mgoegel/ec1834-fdc-board/EC1834_FDC.kicad_sch

## KiCad design EC1834_FDC.kicad_sch (2025-08-20)

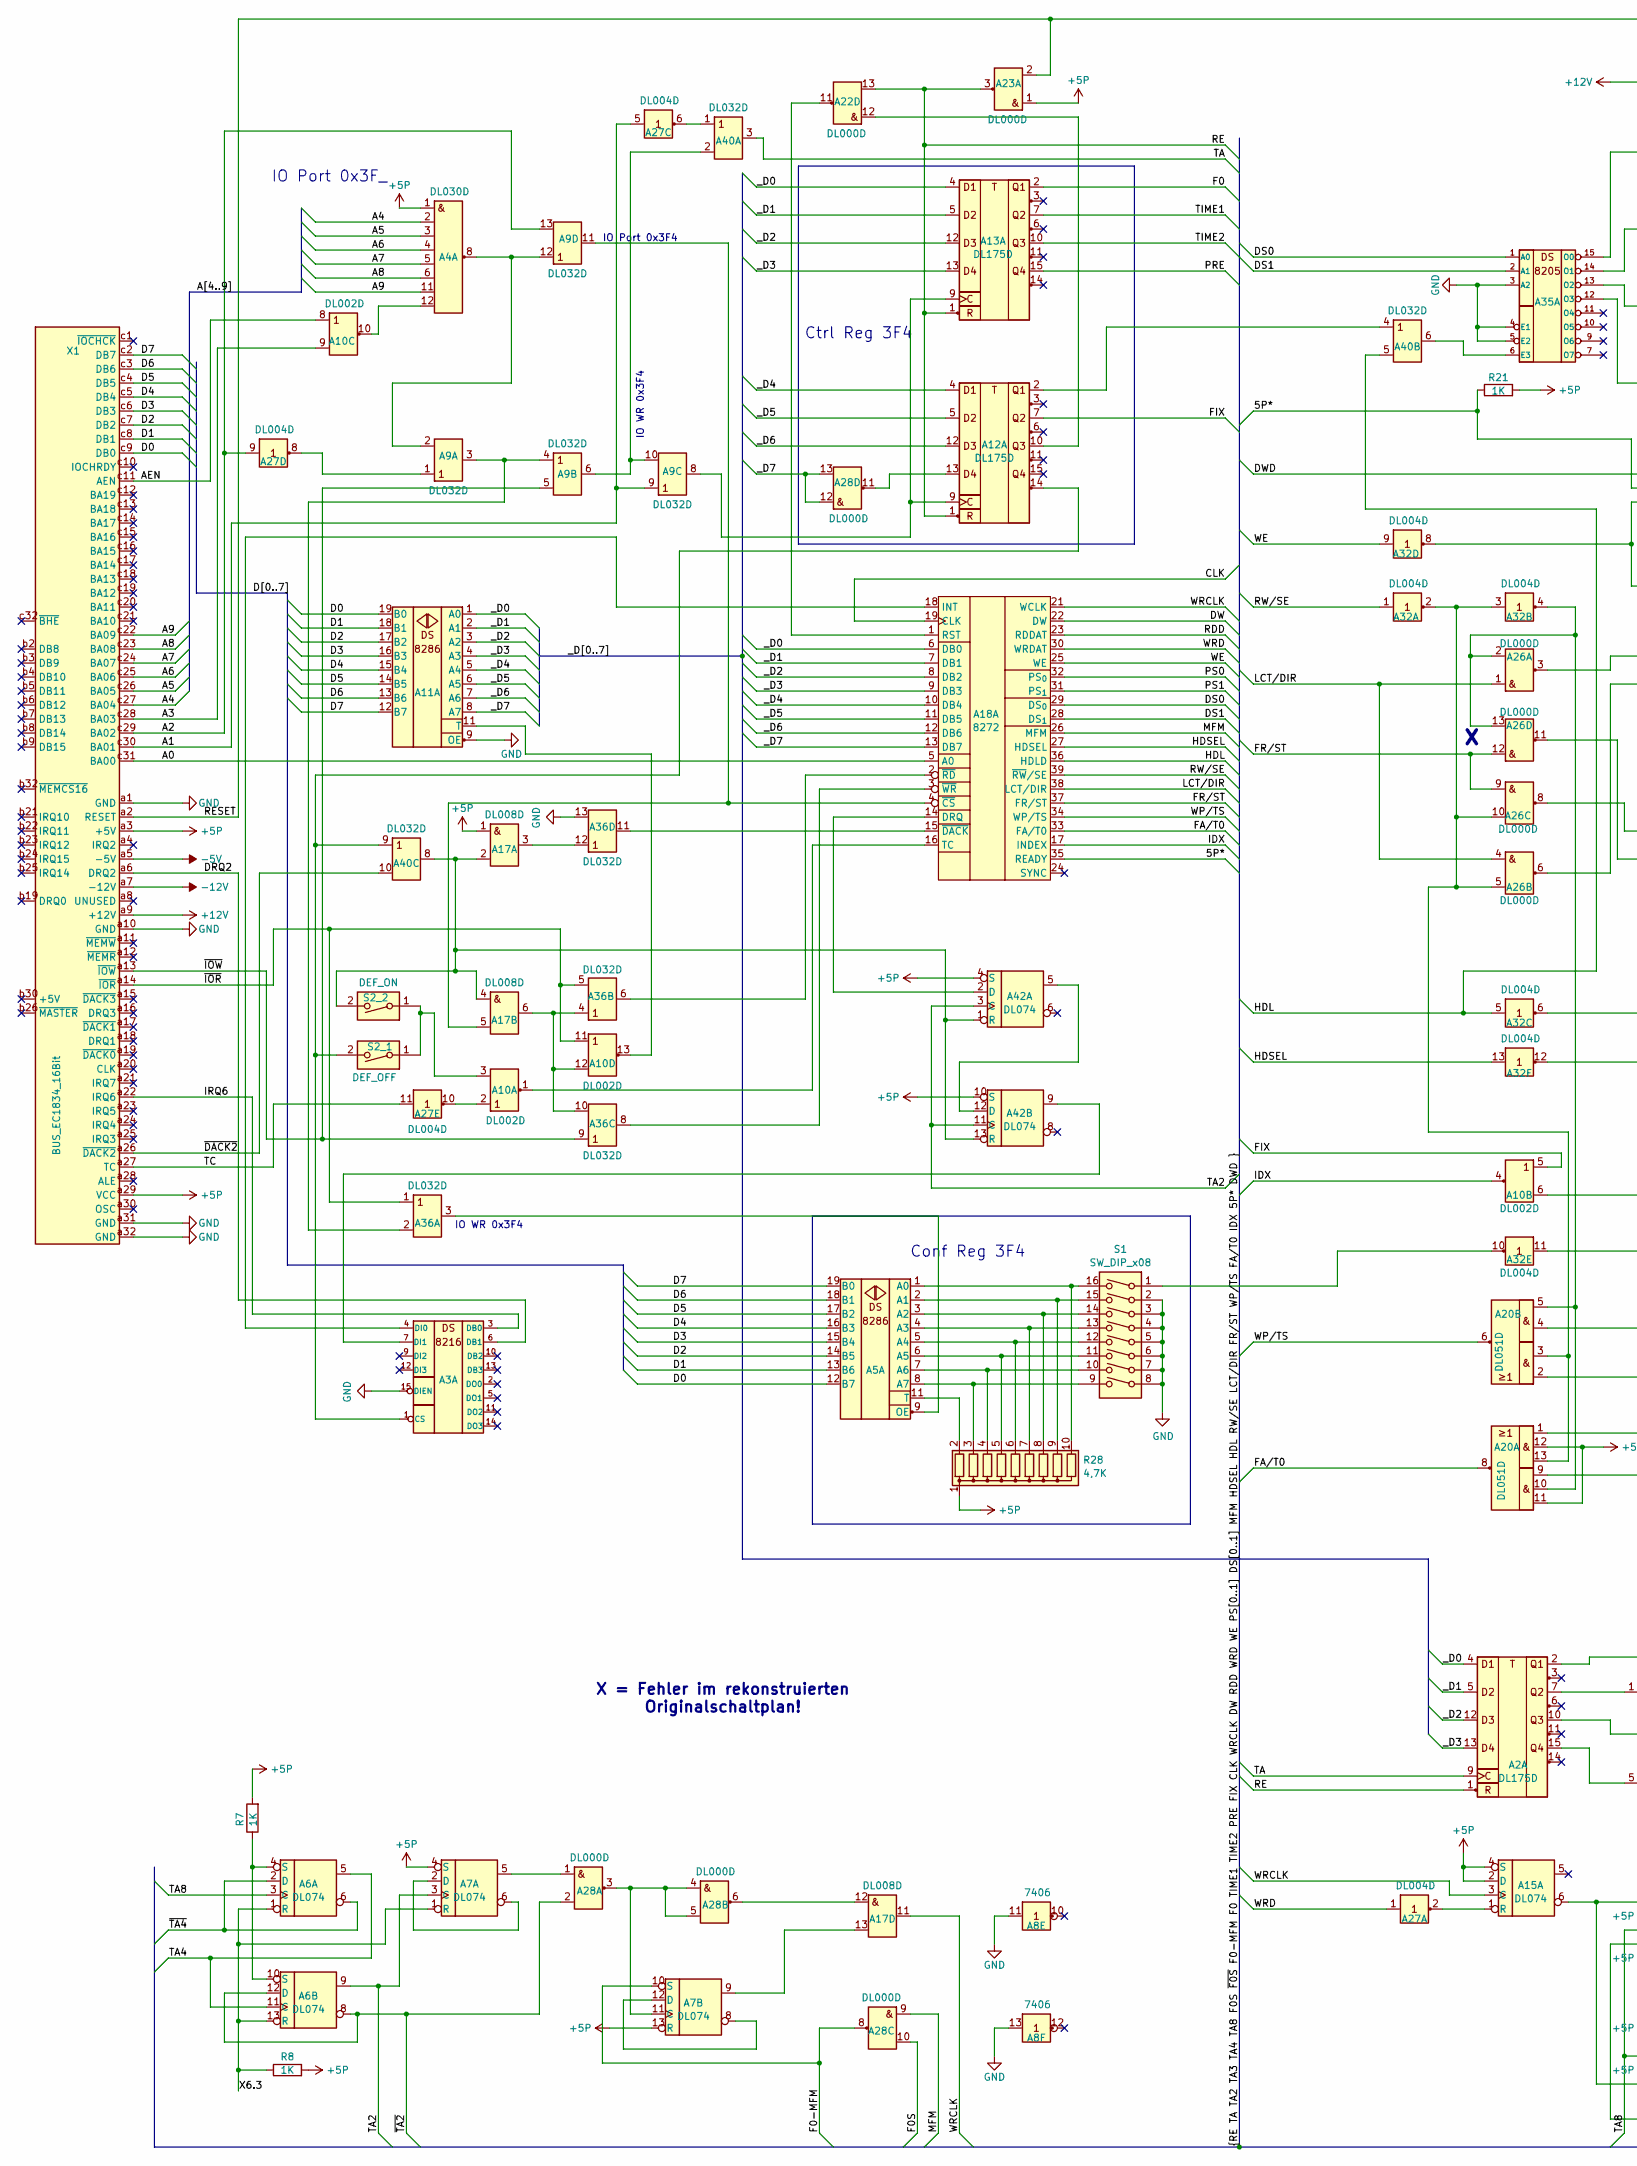
[picture p4: schematic EC1834_FDC.kicad_sch, part in row 1, column 1]

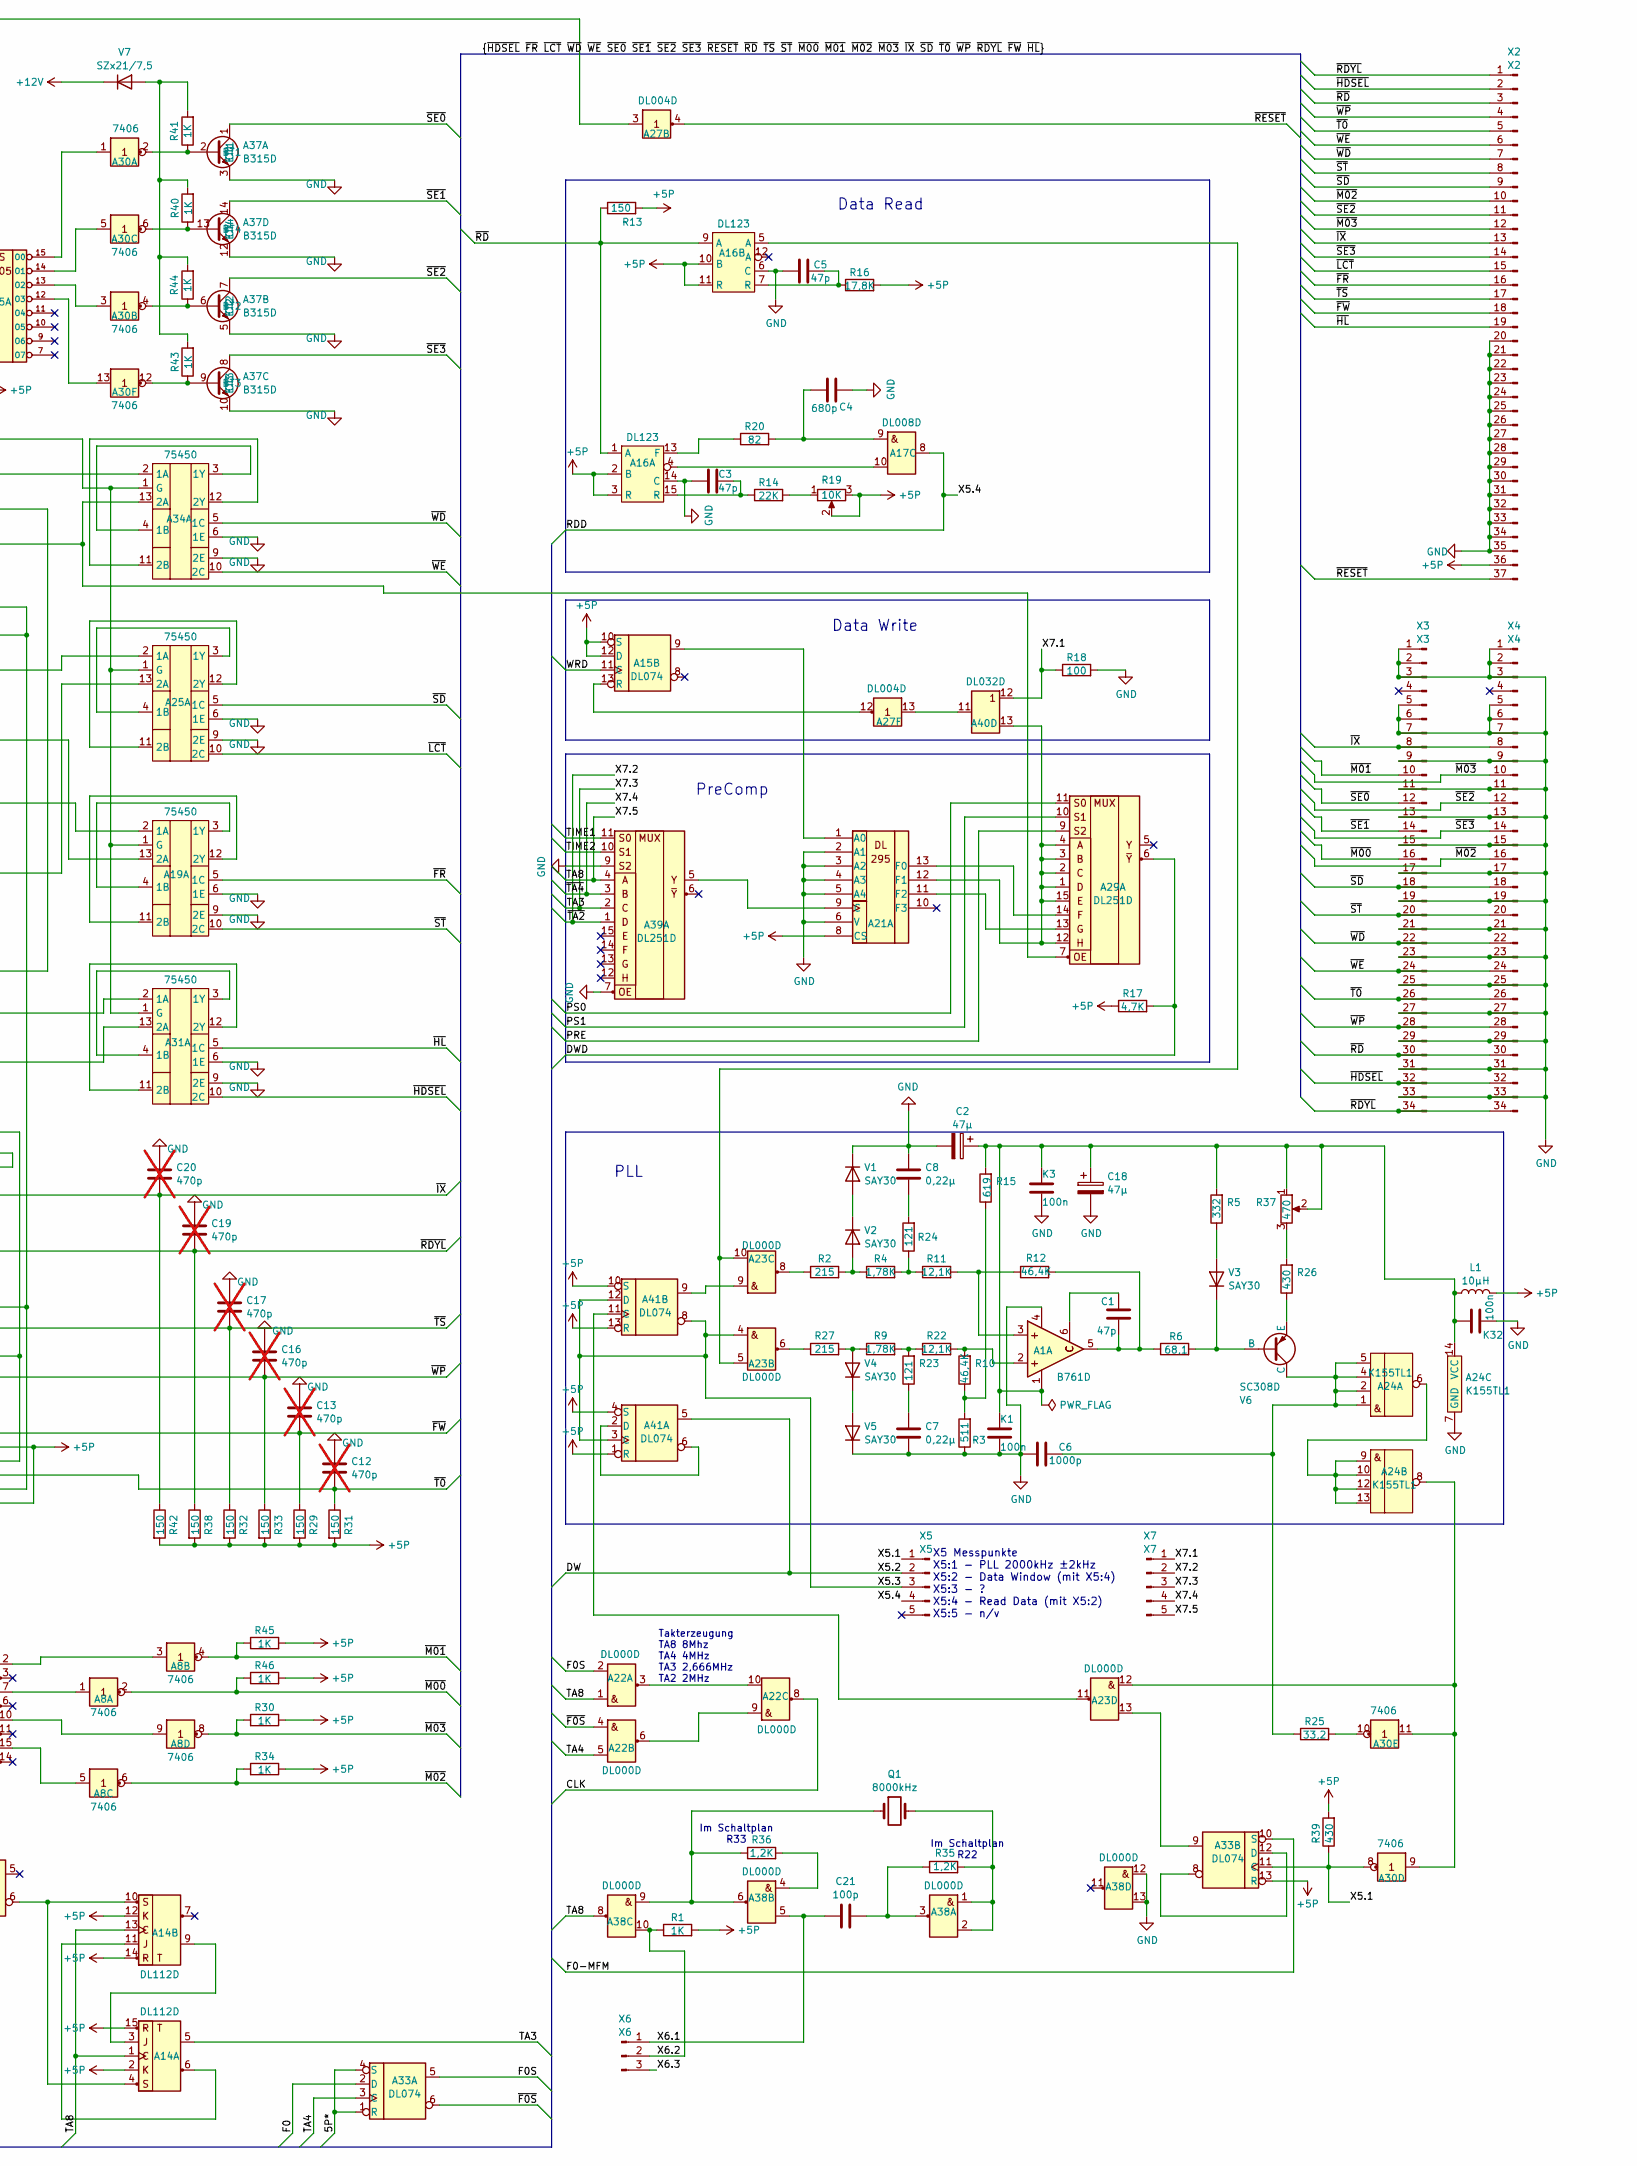
[picture p5: schematic EC1834_FDC.kicad_sch, part in row 1, column 2]

Parts:
A1: B761D; DIP-6_W7.62mm
A2, A12, A13: DL175D; DIP-16_W7.62mm
A3: DS8216; DIP-16_W7.62mm
A4: DL030D; DIP-14_W7.62mm
A5, A11: DS8286D; DIP-20_W7.62mm
A6, A7, A15, A33, A41, A42: DL074; DIP-14_W7.62mm
A8, A30: 7406; DIP-14_W7.62mm
A9, A36, A40: DL032D; DIP-14_W7.62mm
A10: DL002D; DIP-14_W7.62mm
A14: DL112D; DIP-16_W7.62mm
A16: DL123; DIP-16_W7.62mm
A17: DL008D; DIP-14_W7.62mm
A18: 8272; DIP-40_W15.24mm
A19, A25, A31, A34: 75450; DIP-14_W7.62mm
A20: DL051D; DIP-14_W7.62mm
A21: DL295; DIP-14_W7.62mm
A22, A23, A26, A28, A38: DL000D; DIP-14_W7.62mm
A24: K155TL1; DIP-14_W7.62mm
A27, A32: DL004D; DIP-14_W7.62mm
A29, A39: DL251D; DIP-16_W7.62mm
A35: DS8205; DIP-16_W7.62mm
A37: B315D; DIP-14_W7.62mm
C1, C3, C5: 47p; C_Disc_D4.3mm_W1.9mm_P5.00mm
C2, C18: 47µ; CP_Radial_Tantal_D5.0mm_P5.00mm
C4: 680p; C_Disc_D4.3mm_W1.9mm_P5.00mm
C6: 1000p; CP_Axial_L11.0mm_D5.0mm_P18.00mm_Horizontal
C7, C8: 0,22µ; CP_Axial_L18.0mm_D6.5mm_P25.00mm_Horizontal
C12, C13, C16, C17, C19, C20: 470p; C_Disc_D4.3mm_W1.9mm_P5.00mm; not fitted
C21: 100p; C_Disc_D4.3mm_W1.9mm_P5.00mm
K1, K3, K32: 100n; C_Disc_D4.3mm_W1.9mm_P5.00mm
L1: 10µH; L_Axial_L9.5mm_D4.0mm_P12.70mm_Horizontal_Fastron_SMCC
Q1: 8000kHz; Crystal_HC49-U_Horizontal
R1, R7, R8, R21, R30, R34, R40, R41, R43, R44, R45, R46: 1K; R_Axial_L9.0mm_D1.8mm_P12.70mm_Horizontal
R2, R27: 215; R_Axial_L9.0mm_D1.8mm_P12.70mm_Horizontal
R3: 511; R_Axial_L9.0mm_D1.8mm_P12.70mm_Horizontal
R4, R9: 1,78K; R_Axial_L9.0mm_D1.8mm_P12.70mm_Horizontal
R5: 332; R_Axial_L9.0mm_D1.8mm_P12.70mm_Horizontal
R6: 68,1; R_Axial_L9.0mm_D1.8mm_P12.70mm_Horizontal
R10, R12: 46,4K; R_Axial_L9.0mm_D1.8mm_P12.70mm_Horizontal
R11, R22: 12,1K; R_Axial_L9.0mm_D1.8mm_P12.70mm_Horizontal
R13, R29, R31, R32, R33, R38, R42: 150; R_Axial_L9.0mm_D1.8mm_P12.70mm_Horizontal
R14: 22K; R_Axial_L9.0mm_D1.8mm_P12.70mm_Horizontal
R15: 619; R_Axial_L9.0mm_D1.8mm_P12.70mm_Horizontal
R16: 17,8K; R_Axial_L9.0mm_D1.8mm_P12.70mm_Horizontal
R17: 4,7K; R_Axial_L9.0mm_D1.8mm_P12.70mm_Horizontal
R18: 100; R_Axial_L9.0mm_D1.8mm_P12.70mm_Horizontal
R19: 10K; Potentiometer_ACP_CA6-H2,5_Horizontal
R20: 82; R_Axial_L9.0mm_D1.8mm_P12.70mm_Horizontal
R23, R24: 121; R_Axial_L9.0mm_D1.8mm_P12.70mm_Horizontal
R25: 33,2; R_Axial_L9.0mm_D1.8mm_P12.70mm_Horizontal
R26, R39: 430; R_Axial_L9.0mm_D1.8mm_P12.70mm_Horizontal
R28: 4,7K; R_Array_SIP10
R35, R36: 1,2K; R_Axial_L9.0mm_D1.8mm_P12.70mm_Horizontal
R37: 470; Potentiometer_ACP_CA6-H2,5_Horizontal
S1: SW_DIP_x08; SW_DIP_SPSTx08_Slide_6.7x21.88mm_W7.62mm_P2.54mm_LowProfile
S2_1: DEF_OFF; SW_DIP_SPSTx01_Slide_9.78x4.72mm_W7.62mm_P2.54mm
S2_2: DEF_ON; SW_DIP_SPSTx01_Slide_9.78x4.72mm_W7.62mm_P2.54mm
V1, V2, V3, V4, V5: SAY30; TO-92-2
V6: SC308D; TO-92_Inline_Wide
V7: SZx21/7,5; TO-92-2
X1: BUS_EC1834_16Bit; DIN41612_C_3x32_Male_Horizontal_THT
X2: X2; DSUB-37_Socket_Horizontal_P2.77x2.84mm_EdgePinOffset9.90mm_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
X3: X3; IDC-Header_2x17_P2.54mm_Vertical
X4: X4; IDC-Header_2x17_P2.54mm_Vertical
X5: X5; Molex_KK-254_AE-6410-05A_1x05_P2.54mm_Vertical
X6: X6; Molex_KK-254_AE-6410-03A_1x03_P2.54mm_Vertical
X7: X7; Molex_KK-254_AE-6410-05A_1x05_P2.54mm_Vertical

Connections:
5P*: A18.35 (READY), A19.1 (G), A25.1 (G), A31.1 (G), A33.1 (R), A33.4 (S), A34.1 (G), R21.1
+5P: A4.1 (A), A7.4 (S), A7.13 (R), A14.2 (K1), A14.12 (K2), A14.14 (R2), A14.15 (R1), A15.2 (D), A15.4 (S), A15.10 (S), A15.12 (D), A16.2 (B), A16.3 (R), A16.10 (B), A16.11 (R), A17.1 (A1), A20.11 (1F), A20.12 (1B), A21.8 (CS), A23.1 (A1), A33.13 (R), A41.1 (R), A41.4 (S), A41.10 (S), A41.13 (R), A42.4 (S), A42.10 (S), L1.2, R1.2, R7.2, R8.2, R13.2, R16.2, R17.1, R19.2, R19.3, R21.2, R28.1 (common), R29.2, R30.1, R31.2, R32.2, R33.2, R34.1, R38.2, R39.2, R42.2, R45.2, R46.2, X1.a3 (+5V), X1.a29 (VCC), X2.36
+12V: V7.1 (K), X1.a9 (+12V)
-5V: X1.a5 (-5V)
-12V: X1.a7 (-12V)
A0: A18.5 (A0), X1.c31 (BA00)
A1: A9.9 (A3), A27.5 (A3), X1.c30 (BA01)
A2: A9.13 (B4), A27.9 (A4), X1.c29 (BA02)
A3: A10.9 (B3), X1.c28 (BA03)
A4: A4.2 (B), X1.c27 (BA04)
A5: A4.3 (C), X1.c26 (BA05)
A6: A4.4 (D), X1.c25 (BA06)
A7: A4.5 (E), X1.c24 (BA07)
A8: A4.6 (F), X1.c23 (BA08)
A9: A4.11 (G), X1.c22 (BA09)
AEN: A10.8 (A3), X1.c11 (AEN)
CLK: A18.19 (CLK), A22.8 (Y3)
D0: A5.12 (B7), A11.19 (B0), X1.c9 (DB0)
D1: A5.13 (B6), A11.18 (B1), X1.c8 (DB1)
D2: A5.14 (B5), A11.17 (B2), X1.c7 (DB2)
D3: A5.15 (B4), A11.16 (B3), X1.c6 (DB3)
D4: A5.16 (B3), A11.15 (B4), X1.c5 (DB4)
D5: A5.17 (B2), A11.14 (B5), X1.c4 (DB5)
D6: A5.18 (B1), A11.13 (B6), X1.c3 (DB6)
D7: A5.19 (B0), A11.12 (B7), X1.c2 (DB7)
DRQ2: A3.6 (DB1), X1.a6 (DRQ2)
DS0: A18.29 (DS_{0}), A35.1 (A0)
DS1: A18.28 (DS_{1}), A35.2 (A1)
DW: A18.22 (DW), A41.5, X5.2
DWD: A29.6 (~Y), A34.2 (1A), R17.2
F0: A13.2 (Q1), A33.2 (D)
F0-MFM: A7.10 (S), A28.8 (Y3), A33.10 (S)
F0S: A22.2 (B1), A28.10 (B3), A33.5
FA/T0: A18.33 (FA/T0), A20.8 (1Y)
FIX: A10.5 (A2), A12.7 (Q2)
FR/ST: A18.37 (FR/ST), A26.9 (A3), A26.12 (A4)
GND: A1.4 (-), A3.15 (DIEN), A8.11 (A5), A8.13 (A6), A11.9 (OE), A16.6 (C), A16.14 (C), A19.6 (1E), A19.9 (2E), A21.2 (A1), A21.3 (A2), A21.4 (A3), A21.5 (A4), A21.6 (V), A24.7 (GND), A25.6 (1E), A25.9 (2E), A31.6 (1E), A31.9 (2E), A34.6 (1E), A34.9 (2E), A35.3 (A2), A35.4 (E1), A35.5 (E2), A36.13 (B4), A37.3 (ET1), A37.5 (ET2), A37.10 (ET3), A37.12 (ET4), A38.12 (A4), A38.13 (B4), A39.7 (~OE), A39.9 (S2), C2.2, C3.1, C4.1, C5.1, C6.1, C7.1, C8.1, C12.1, C13.1, C16.1, C17.1, C18.2, C19.1, C20.1, K1.2, K3.2, K32.2, R3.1, R18.2, S1.2, S1.3, S1.4, S1.5, S1.6, S1.7, S1.8, V1.1 (K), V5.1 (K), X1.a1 (GND), X1.a10 (GND), X1.a31 (GND), X1.a32 (GND), X2.20, X2.21, X2.22, X2.23, X2.24, X2.25, X2.26, X2.27, X2.28, X2.29, X2.30, X2.31, X2.32, X2.33, X2.34, X2.35, X3.1, X3.2, X3.3, X3.5, X3.6, X3.7, X3.9, X3.11, X3.13, X3.15, X3.17, X3.19, X3.21, X3.23, X3.25, X3.27, X3.29, X3.31, X3.33, X4.1, X4.2, X4.3, X4.5, X4.6, X4.7, X4.9, X4.11, X4.13, X4.15, X4.17, X4.19, X4.21, X4.23, X4.25, X4.27, X4.29, X4.31, X4.33
HDL: A18.36 (HDLD), A32.5 (A3), A40.5 (B2)
HDSEL: A18.27 (HDSEL), A32.13 (A6)
IDX: A10.4 (Y2), A18.17 (INDEX)
IRQ6: A3.3 (DB0), X1.a22 (IRQ6)
LCT/DIR: A18.38 (LCT/DIR), A26.1 (A1), A26.4 (A2)
MFM: A18.26 (MFM), A28.9 (A3)
unnamed: A1.1 (+), A24.14 (VCC), C2.1, C18.1, K1.1, K3.1, K32.1, L1.1, R5.2, R15.2, R37.1, R37.2
unnamed: A1.2 (+), R10.2, R22.2
unnamed: A1.3 (-), R11.2, R12.1
unnamed: A1.5, C1.2, R6.1, R12.2
unnamed: A1.6 (C), C1.1
unnamed: A2.2 (Q1), A8.3 (A2)
unnamed: A2.7 (Q2), A8.1 (A1)
unnamed: A2.10 (Q3), A8.9 (A4)
unnamed: A2.15 (Q4), A8.5 (A3)
unnamed: A3.7 (DI1), A42.9
unnamed: A4.8 (Y), A9.2 (B1), A9.12 (A4)
unnamed: A5.1 (A0), R28.10 (R9), S1.16
unnamed: A5.2 (A1), R28.9 (R8), S1.15
unnamed: A5.3 (A2), R28.8 (R7), S1.14
unnamed: A5.4 (A3), R28.7 (R6), S1.13
unnamed: A5.5 (A4), R28.6 (R5), S1.12
unnamed: A5.6 (A5), R28.5 (R4), S1.11
unnamed: A5.7 (A6), R28.4 (R3), S1.10
unnamed: A5.8 (A7), R28.3 (R2), S1.9
unnamed: A5.11 (T), R28.2 (R1)
unnamed: A6.4 (S), A6.10 (S), R7.1
unnamed: A7.2 (D), A7.6
unnamed: A7.8, A7.12 (D)
unnamed: A10.1 (Y1), A18.16 (TC)
unnamed: A10.2 (A1), A27.10 (Y5)
unnamed: A10.3 (B1), S2_1.1, S2_2.1
unnamed: A4.12 (H), A10.10 (Y3)
unnamed: A10.12 (B4), A17.6 (Y2), A36.4 (A2), A36.10 (B3)
unnamed: A10.13 (Y4), A11.11 (T)
unnamed: A12.2 (Q1), A40.4 (A2)
unnamed: A9.8 (Y3), A12.9 (C), A13.9 (C)
unnamed: A12.10 (Q3), A22.12 (A4)
unnamed: A12.13 (D4), A28.11 (Y4)
unnamed: A3.1 (CS), A12.14 (~Q4), A40.9 (A3), S2_1.2
unnamed: A14.3 (J1), A14.9 (Q2)
unnamed: A14.4 (S1), A14.10 (S2), A15.6
unnamed: A14.6 (/Q1), A14.11 (J2)
unnamed: A15.1 (R), A27.2 (Y1)
unnamed: A15.9, A21.1 (A0)
unnamed: A15.13 (R), A27.12 (Y6)
unnamed: A16.4, A17.10 (B3)
unnamed: A16.5 (A), A23.5 (B2), A23.10 (B3)
unnamed: A16.7 (R), C5.2, R16.1
unnamed: A16.13 (F), R20.1
unnamed: A16.15 (R), C3.2, R14.1
unnamed: A17.2 (B1), A17.4 (A2), A40.8 (Y3), A42.1 (R), A42.13 (R), S2_2.2
unnamed: A17.3 (Y1), A36.12 (A4)
unnamed: A9.11 (Y4), A17.5 (B2), A18.4 (~CS)
unnamed: A17.9 (A3), C4.2, R20.2
unnamed: A17.12 (A4), A28.6 (Y2)
unnamed: A7.9, A17.13 (B4)
unnamed: A18.1 (RST), A22.11 (Y4)
unnamed: A18.2 (~RD), A36.6 (Y2)
unnamed: A18.3 (~WR), A36.8 (Y3)
unnamed: A18.14 (DRQ), A42.2 (D)
unnamed: A18.15 (~DACK), A36.11 (Y4)
unnamed: A3.4 (DI0), A18.18 (INT)
unnamed: A19.2 (1A), A26.8 (Y3)
unnamed: A19.3 (1Y), A19.4 (1B)
unnamed: A19.11 (2B), A19.12 (2Y)
unnamed: A19.13 (2A), A26.11 (Y4)
unnamed: A20.5 (2E), A20.10 (1E), A26.2 (B1), A26.13 (B4), A32.4 (Y2)
unnamed: A20.3 (2B), A20.13 (1C), A26.5 (B2), A26.10 (B3), A32.2 (Y1), A32.3 (A2)
unnamed: A21.9 (C), A39.5 (Y)
unnamed: A21.11 (F2), A29.13 (G)
unnamed: A21.12 (F1), A29.1 (D), A29.2 (C), A29.3 (B), A29.4 (A), A29.12 (H), A29.15 (E), A40.13 (B4)
unnamed: A21.13 (F0), A29.14 (F)
unnamed: A22.6 (Y2), A22.9 (A3)
unnamed: A22.3 (Y1), A22.10 (B3)
unnamed: A23.6 (Y2), R27.1
unnamed: A23.8 (Y3), R2.1
unnamed: A23.9 (A3), A41.9
unnamed: A23.11 (Y4), A41.11 (C)
unnamed: A23.12 (A4), A24.8, A30.9 (A4), A30.11 (A5)
unnamed: A23.13 (B4), A33.9
unnamed: A24.1, A24.2, A24.4, A24.5, C6.2, R25.1, V6.1 (C)
unnamed: A24.6, A24.9, A24.10, A24.12, A24.13
unnamed: A25.2 (1A), A26.3 (Y1)
unnamed: A25.3 (1Y), A25.4 (1B)
unnamed: A25.11 (2B), A25.12 (2Y)
unnamed: A25.13 (2A), A26.6 (Y2)
unnamed: A27.6 (Y3), A40.1 (A1)
unnamed: A9.1 (A1), A27.8 (Y4)
unnamed: A27.13 (A6), A40.11 (Y4)
unnamed: A7.5, A28.1 (A1)
unnamed: A7.11 (C), A28.3 (Y1), A28.4 (A2), A28.5 (B2)
unnamed: A29.7 (~OE), A32.8 (Y4), A34.13 (2A)
unnamed: A30.1 (A1), A35.15 (O0)
unnamed: A30.2 (Y1), A37.2 (BT1), R41.1
unnamed: A30.3 (A2), A35.13 (O2)
unnamed: A30.4 (Y2), A37.6 (BT2), R44.1
unnamed: A30.5 (A3), A35.14 (O1)
unnamed: A30.6 (Y3), A37.13 (BT4), R40.1
unnamed: A30.10 (Y5), R25.2
unnamed: A30.12 (Y6), A37.9 (BT3), R43.1
unnamed: A30.13 (A6), A35.12 (O3)
unnamed: A31.2 (1A), A32.6 (Y3)
unnamed: A31.3 (1Y), A31.4 (1B)
unnamed: A31.11 (2B), A31.12 (2Y)
unnamed: A31.13 (2A), A32.12 (Y6)
unnamed: A32.10 (Y5), S1.1
unnamed: A33.8, A33.12 (D)
unnamed: A34.3 (1Y), A34.4 (1B)
unnamed: A34.11 (2B), A34.12 (2Y)
unnamed: A35.6 (E3), A40.6 (Y2)
unnamed: A9.3 (Y1), A9.4 (A2), A36.2 (B1)
unnamed: A5.9 (OE), A36.3 (Y1)
unnamed: A38.1 (A1), A38.2 (B1), Q1.2, R35.2
unnamed: A38.3 (Y1), C21.2, R35.1
unnamed: A38.4 (A2), R36.2
unnamed: A38.6 (Y2), A38.9 (A3), Q1.1, R36.1
unnamed: A9.6 (Y2), A9.10 (B3), A40.2 (B1)
unnamed: A41.2 (D), A41.6
unnamed: A42.5, A42.12 (D)
unnamed: C7.2, R23.1
unnamed: C8.2, R24.2
unnamed: R2.2, R4.1, V2.2 (A)
unnamed: R5.1, V3.2 (A)
unnamed: R6.2, V3.1 (K), V6.2 (B)
unnamed: R3.2, R10.1, R15.1
unnamed: R4.2, R11.1, R24.1
unnamed: R14.2, R19.1
unnamed: R9.2, R22.1, R23.2
unnamed: R26.1, V6.3 (E)
unnamed: R26.2, R37.3
unnamed: R9.1, R27.2, V4.2 (A)
unnamed: R40.2, R41.2, R43.2, R44.2, V7.2 (A)
unnamed: V1.2 (A), V2.1 (K)
unnamed: V4.1 (K), V5.2 (A)
PRE: A13.15 (Q4), A29.9 (S2)
PS0: A18.32 (PS_{0}), A29.11 (S0)
PS1: A18.31 (PS_{1}), A29.10 (S1)
RDD: A17.8 (Y3), A18.23 (RDDAT), X5.4
RE: A2.1 (R), A12.1 (R), A13.1 (R), A22.13 (B4), A23.3 (Y1)
RESET: A23.2 (B1), A27.3 (A2), X1.a2 (RESET)
RW/SE: A18.39 (~RW/SE), A32.1 (A1)
TA: A2.9 (C), A40.3 (Y1)
TA2: A6.9, A7.3 (C), A42.3 (C), A42.11 (C)
TA3: A14.5 (Q1), A39.2 (C), X7.3
TA4: A6.5, A6.11 (C), A22.5 (B2), A33.3 (C)
TA8: A6.3 (C), A14.1 (C1), A14.13 (C2), A22.1 (A1), A38.8 (Y3), A39.4 (A), X7.5
TC: A27.11 (A5), X1.a27 (TC)
TIME1: A13.7 (Q2), A39.11 (S0)
TIME2: A13.10 (Q3), A39.10 (S1)
WE: A18.25 (WE), A32.9 (A4)
WP/TS: A18.34 (WP/TS), A20.6 (2Y)
WRCLK: A15.3 (C), A17.11 (Y4), A18.21 (WCLK)
WRD: A15.11 (C), A18.30 (WRDAT), A27.1 (A1)
X5.1: A30.8 (Y4), A33.11 (C), R39.1, X5.1
X5.3: A23.4 (A2), A41.3 (C), A41.8, A41.12 (D), X5.3
X6.1: A38.5 (B2), C21.1, X6.1
X6.2: A38.10 (B3), R1.1, X6.2
X6.3: A6.1 (R), A6.13 (R), A7.1 (R), R8.1, X6.3
X7.1: A40.12 (A4), R18.1, X7.1
X7.2: A6.8, A6.12 (D), A28.2 (B1), A39.1 (D), X7.2
X7.4: A6.2 (D), A6.6, A39.3 (B), X7.4
_D0: A2.4 (D1), A11.1 (A0), A13.4 (D1), A18.6 (DB0)
_D1: A2.5 (D2), A11.2 (A1), A13.5 (D2), A18.7 (DB1)
_D2: A2.12 (D3), A11.3 (A2), A13.12 (D3), A18.8 (DB2)
_D3: A2.13 (D4), A11.4 (A3), A13.13 (D4), A18.9 (DB3)
_D4: A11.5 (A4), A12.4 (D1), A18.10 (DB4)
_D5: A11.6 (A5), A12.5 (D2), A18.11 (DB5)
_D6: A11.7 (A6), A12.12 (D3), A18.12 (DB6)
_D7: A11.8 (A7), A18.13 (DB7), A28.12 (A4), A28.13 (B4)
~DACK2: A40.10 (B3), X1.a26 (~DACK2)
~F0S: A22.4 (A2), A33.6
~FR: A19.5 (1C), X2.16
~FW: A20.1 (1A), C13.2, R29.1, X2.18
~HDSEL: A31.10 (2C), X2.2, X3.32, X4.32
~HL: A31.5 (1C), X2.19
~IOR: A10.11 (A4), A36.1 (A1), A36.5 (B2), X1.a14 (~IOR)
~IOW: A9.5 (B2), A36.9 (A3), X1.a13 (~IOW)
~IX: A10.6 (B2), C20.2, R42.1, X2.13, X3.8, X4.8
~LCT: A25.10 (2C), X2.15
~M00: A8.2 (Y1), R46.1, X3.16
~M01: A8.4 (Y2), R45.1, X3.10
~M02: A8.6 (Y3), R34.2, X2.10, X4.16
~M03: A8.8 (Y4), R30.2, X2.12, X4.10
~RDYL: A32.11 (A5), C19.2, R38.1, X2.1, X3.34, X4.34
~RD: A16.1 (A), A16.9 (A), R13.1, X2.3, X3.30, X4.30
~RESET: A27.4 (Y2), X2.37
~SD: A25.5 (1C), X2.9, X3.18, X4.18
~SE0: A37.1 (CT1), X3.12
~SE1: A37.14 (CT4), X3.14
~SE2: A37.7 (CT2), X2.11, X4.12
~SE3: A37.8 (CT3), X2.14, X4.14
~ST: A19.10 (2C), X2.8, X3.20, X4.20
~T0: A20.9 (1D), C12.2, R31.1, X2.5, X3.26, X4.26
~TS: A20.4 (2D), C17.2, R32.1, X2.17
~WD: A34.5 (1C), X2.7, X3.22, X4.22
~WE: A34.10 (2C), X2.6, X3.24, X4.24
~WP: A20.2 (2A), C16.2, R33.1, X2.4, X3.28, X4.28

Notes on the sheet:
IO WR 0x3F4
Im Schaltplan R33
Im Schaltplan R22
IO Port 0x3F4
Conf Reg 3F4
PLL
X5 Messpunkte X5:1 - PLL 2000kHz ±2kHz X5:2 - Data Window (mit X5:4) X5:3 - ? X5:4 - Read Data (mit X5:2) X5:5 - n/v
Takterzeugung TA8 8Mhz TA4 4MHz TA3 2,666MHz TA2 2MHz
PreComp
Data Read
IO Port 0x3F_
X = Fehler im rekonstruierten Originalschaltplan!
Ctrl Reg 3F4
Data Write
