mgoegel/ec1834-fdc-board/Power.kicad_sch

## KiCad design Power.kicad_sch (2025-08-20)

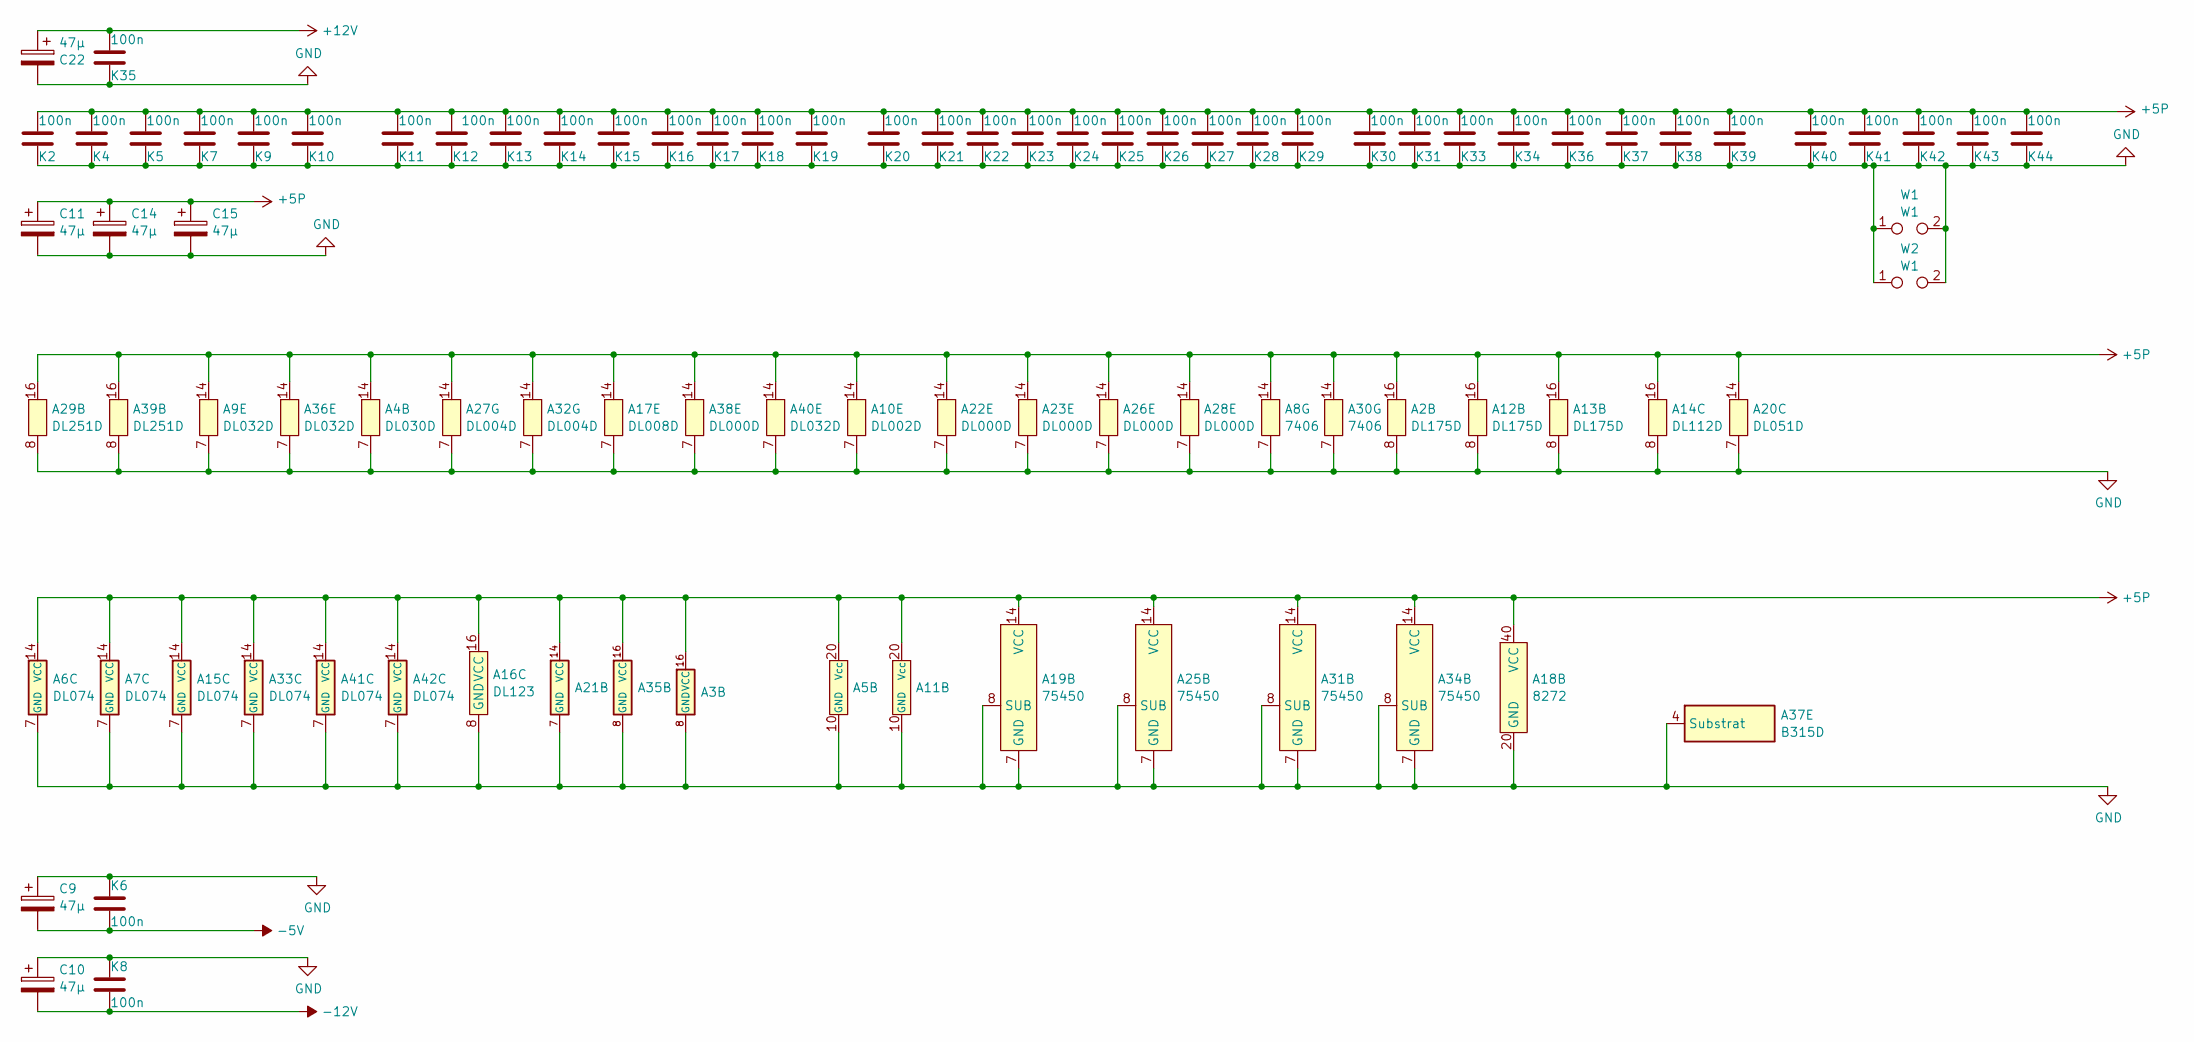
[picture p6: schematic Power.kicad_sch]

Parts:
A2, A12, A13: DL175D; DIP-16_W7.62mm
A3: DS8216; DIP-16_W7.62mm
A4: DL030D; DIP-14_W7.62mm
A5, A11: DS8286D; DIP-20_W7.62mm
A6, A7, A15, A33, A41, A42: DL074; DIP-14_W7.62mm
A8, A30: 7406; DIP-14_W7.62mm
A9, A36, A40: DL032D; DIP-14_W7.62mm
A10: DL002D; DIP-14_W7.62mm
A14: DL112D; DIP-16_W7.62mm
A16: DL123; DIP-16_W7.62mm
A17: DL008D; DIP-14_W7.62mm
A18: 8272; DIP-40_W15.24mm
A19, A25, A31, A34: 75450; DIP-14_W7.62mm
A20: DL051D; DIP-14_W7.62mm
A21: DL295; DIP-14_W7.62mm
A22, A23, A26, A28, A38: DL000D; DIP-14_W7.62mm
A27, A32: DL004D; DIP-14_W7.62mm
A29, A39: DL251D; DIP-16_W7.62mm
A35: DS8205; DIP-16_W7.62mm
A37: B315D; DIP-14_W7.62mm
C9, C10, C11, C14, C15, C22: 47µ; CP_Radial_Tantal_D5.0mm_P5.00mm
K2, K4, K5, K6, K7, K8, K9, K10, K11, K12, K13, K14, K15, K16, K17, K18, K19, K20, K21, K22, K23, K24, K25, K26, K27, K28, K29, K30, K31, K33, K34, K35, K36, K37, K38, K39, K40, K41, K42, K43, K44: 100n; C_Disc_D4.3mm_W1.9mm_P5.00mm
W1, W2: W1; TestPoint_Bridge_Pitch2.54mm_Drill0.7mm

Connections:
+5P: A2.16 (Vcc), A3.16 (VCC), A4.14 (Vcc), A5.20 (Vcc), A6.14 (VCC), A7.14 (VCC), A8.14 (Vcc), A9.14 (Vcc), A10.14 (Vcc), A11.20 (Vcc), A12.16 (Vcc), A13.16 (Vcc), A14.16 (Vcc), A15.14 (VCC), A16.16 (VCC), A17.14 (Vcc), A18.40 (VCC), A19.14 (VCC), A20.14 (Vcc), A21.14 (VCC), A22.14 (Vcc), A23.14 (Vcc), A25.14 (VCC), A26.14 (Vcc), A27.14 (Vcc), A28.14 (Vcc), A29.16 (Vcc), A30.14 (Vcc), A31.14 (VCC), A32.14 (Vcc), A33.14 (VCC), A34.14 (VCC), A35.16 (VCC), A36.14 (Vcc), A38.14 (Vcc), A39.16 (Vcc), A40.14 (Vcc), A41.14 (VCC), A42.14 (VCC), C11.1, C14.1, C15.1, K2.2, K4.2, K5.2, K7.2, K9.2, K10.2, K11.2, K12.2, K13.2, K14.2, K15.2, K16.2, K17.2, K18.2, K19.2, K20.2, K21.2, K22.2, K23.2, K24.2, K25.2, K26.2, K27.2, K28.2, K29.2, K30.2, K31.2, K33.2, K34.2, K36.2, K37.2, K38.2, K39.2, K40.2, K41.2, K42.2, K43.2, K44.2
+12V: C22.1, K35.2
-5V: C9.2, K6.2
-12V: C10.2, K8.2
GND: A2.8 (GND), A3.8 (GND), A4.7 (GND), A5.10 (GND), A6.7 (GND), A7.7 (GND), A8.7 (GND), A9.7 (GND), A10.7 (GND), A11.10 (GND), A12.8 (GND), A13.8 (GND), A14.8 (GND), A15.7 (GND), A16.8 (GND), A17.7 (GND), A18.20 (GND), A19.7 (GND), A19.8 (SUB), A20.7 (GND), A21.7 (GND), A22.7 (GND), A23.7 (GND), A25.7 (GND), A25.8 (SUB), A26.7 (GND), A27.7 (GND), A28.7 (GND), A29.8 (GND), A30.7 (GND), A31.7 (GND), A31.8 (SUB), A32.7 (GND), A33.7 (GND), A34.7 (GND), A34.8 (SUB), A35.8 (GND), A36.7 (GND), A37.4 (Substrat), A38.7 (GND), A39.8 (GND), A40.7 (GND), A41.7 (GND), A42.7 (GND), C9.1, C10.1, C11.2, C14.2, C15.2, C22.2, K2.1, K4.1, K5.1, K6.1, K7.1, K8.1, K9.1, K10.1, K11.1, K12.1, K13.1, K14.1, K15.1, K16.1, K17.1, K18.1, K19.1, K20.1, K21.1, K22.1, K23.1, K24.1, K25.1, K26.1, K27.1, K28.1, K29.1, K30.1, K31.1, K33.1, K34.1, K35.1, K36.1, K37.1, K38.1, K39.1, K40.1, K41.1, K42.1, K43.1, K44.1, W1.1, W1.2, W2.1, W2.2
